cy-888/OpeN64/OpeN64/OpeN64.kicad_sch

## KiCad design OpeN64/OpeN64.kicad_sch (2026-04-06)

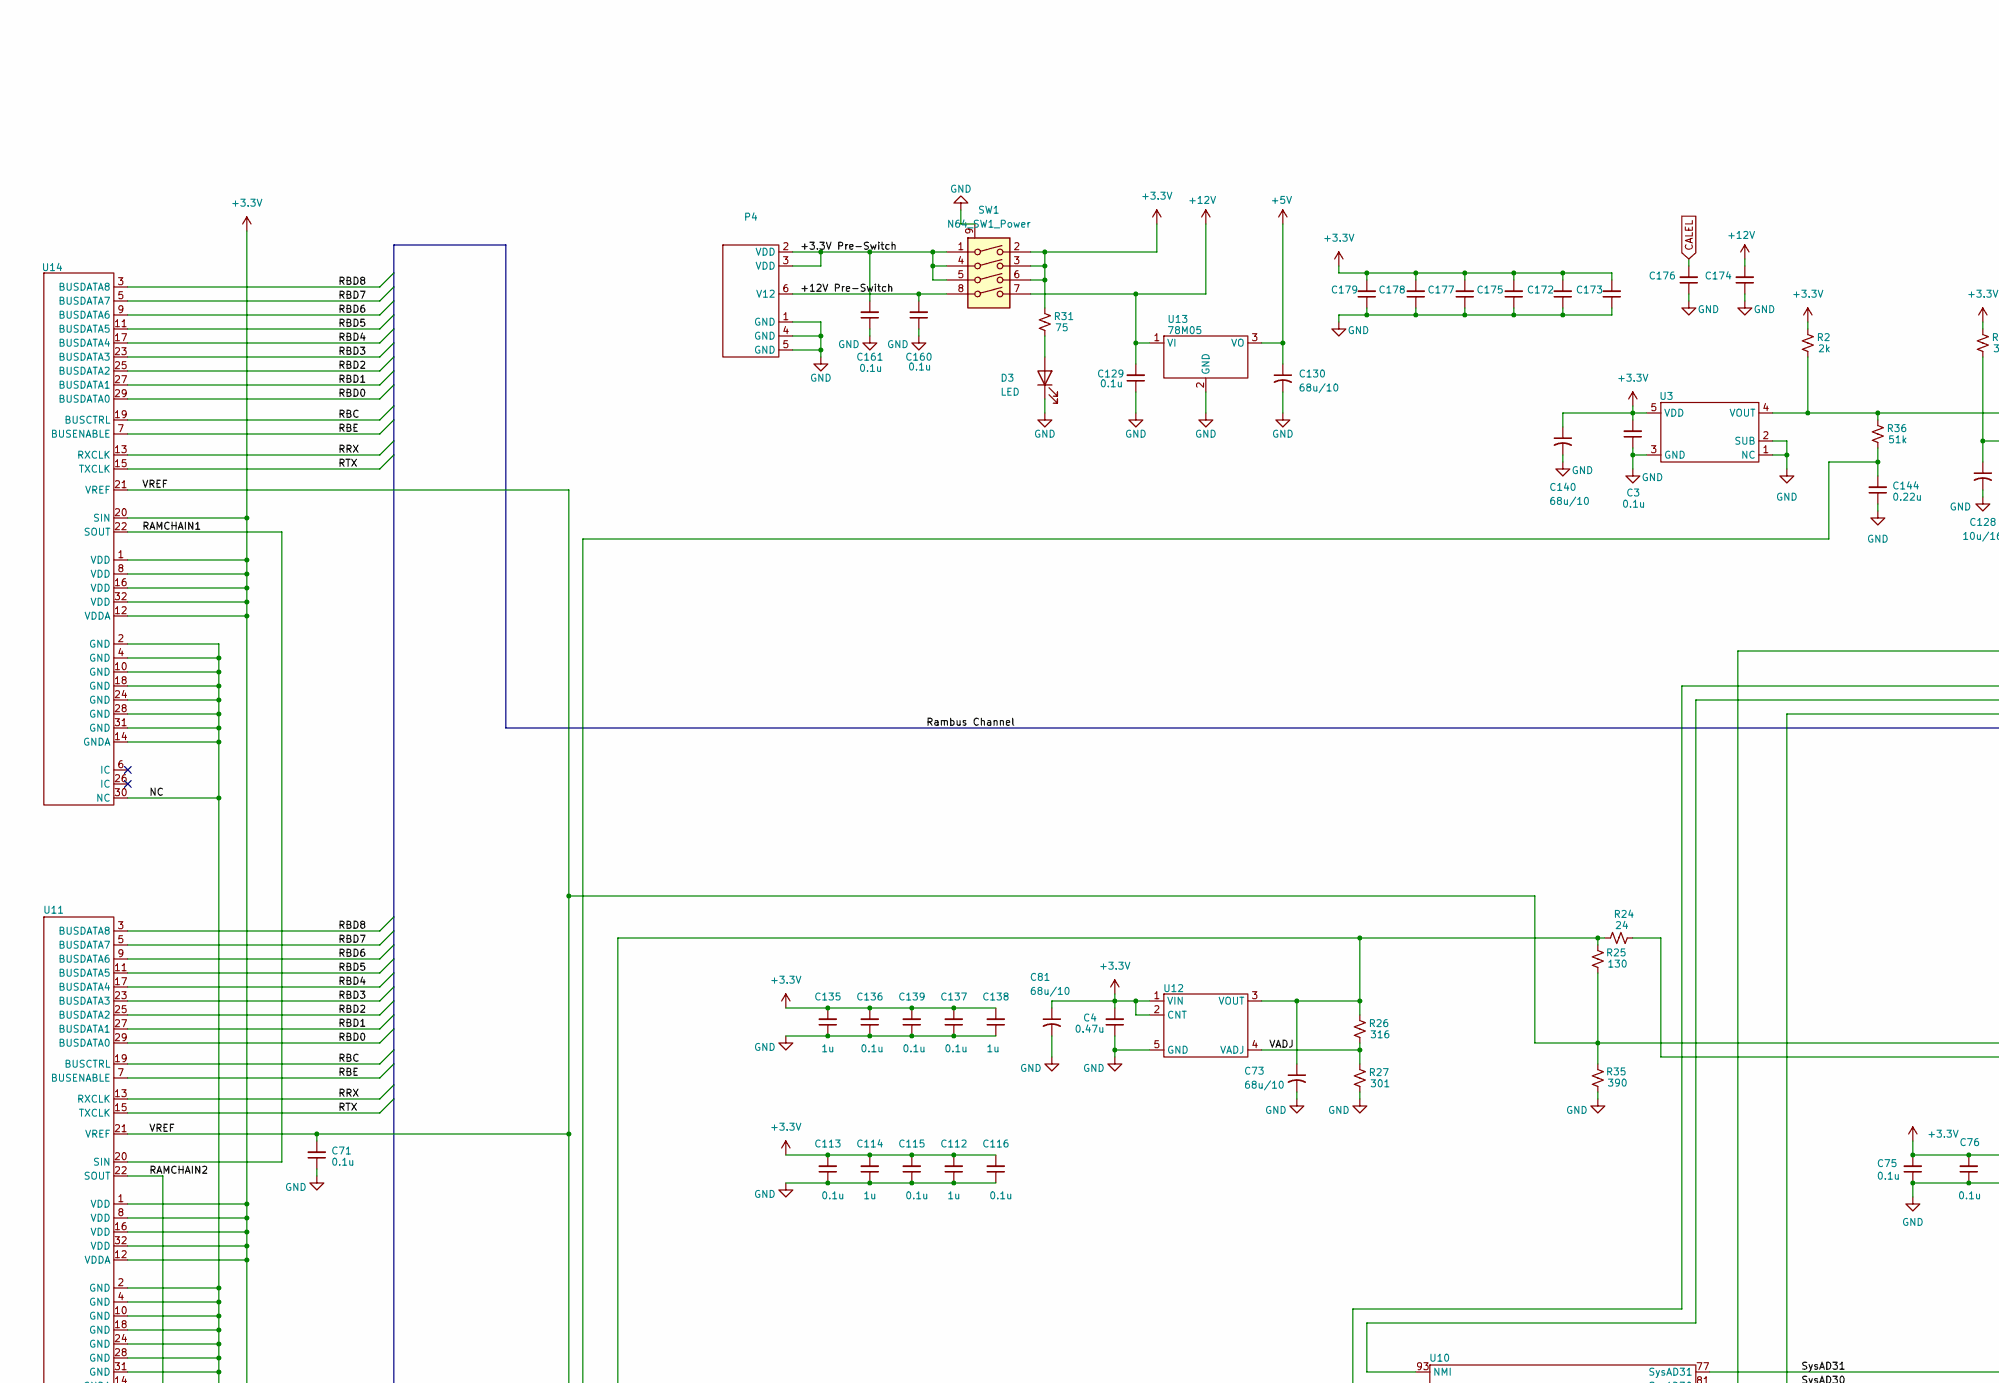
[picture p9: schematic OpeN64.kicad_sch, part in row 1, column 1]

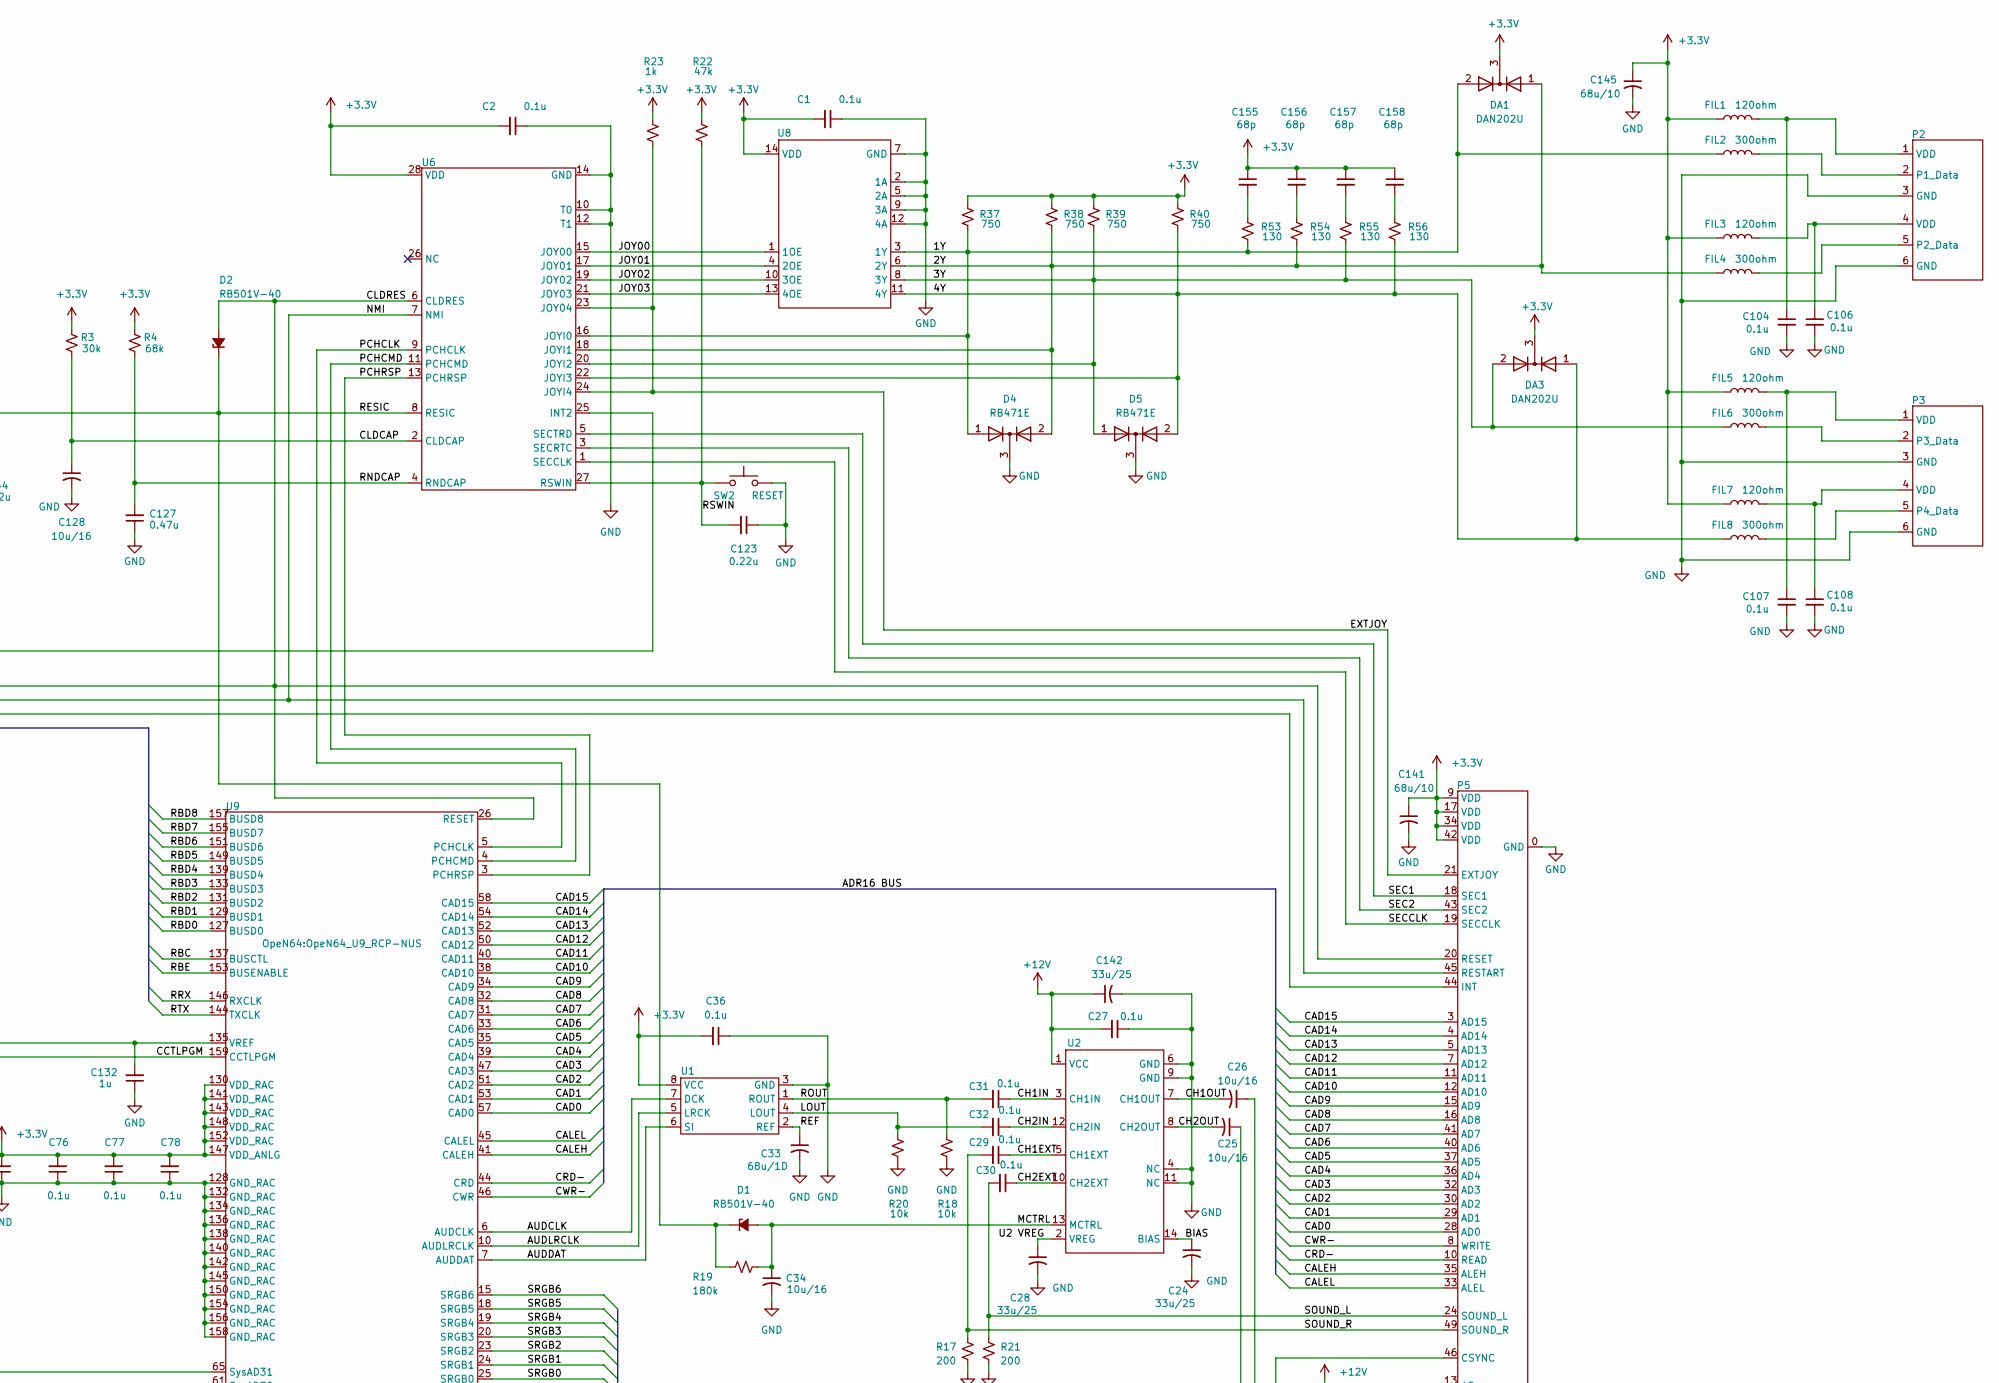
[picture p10: schematic OpeN64.kicad_sch, part in row 1, column 2]

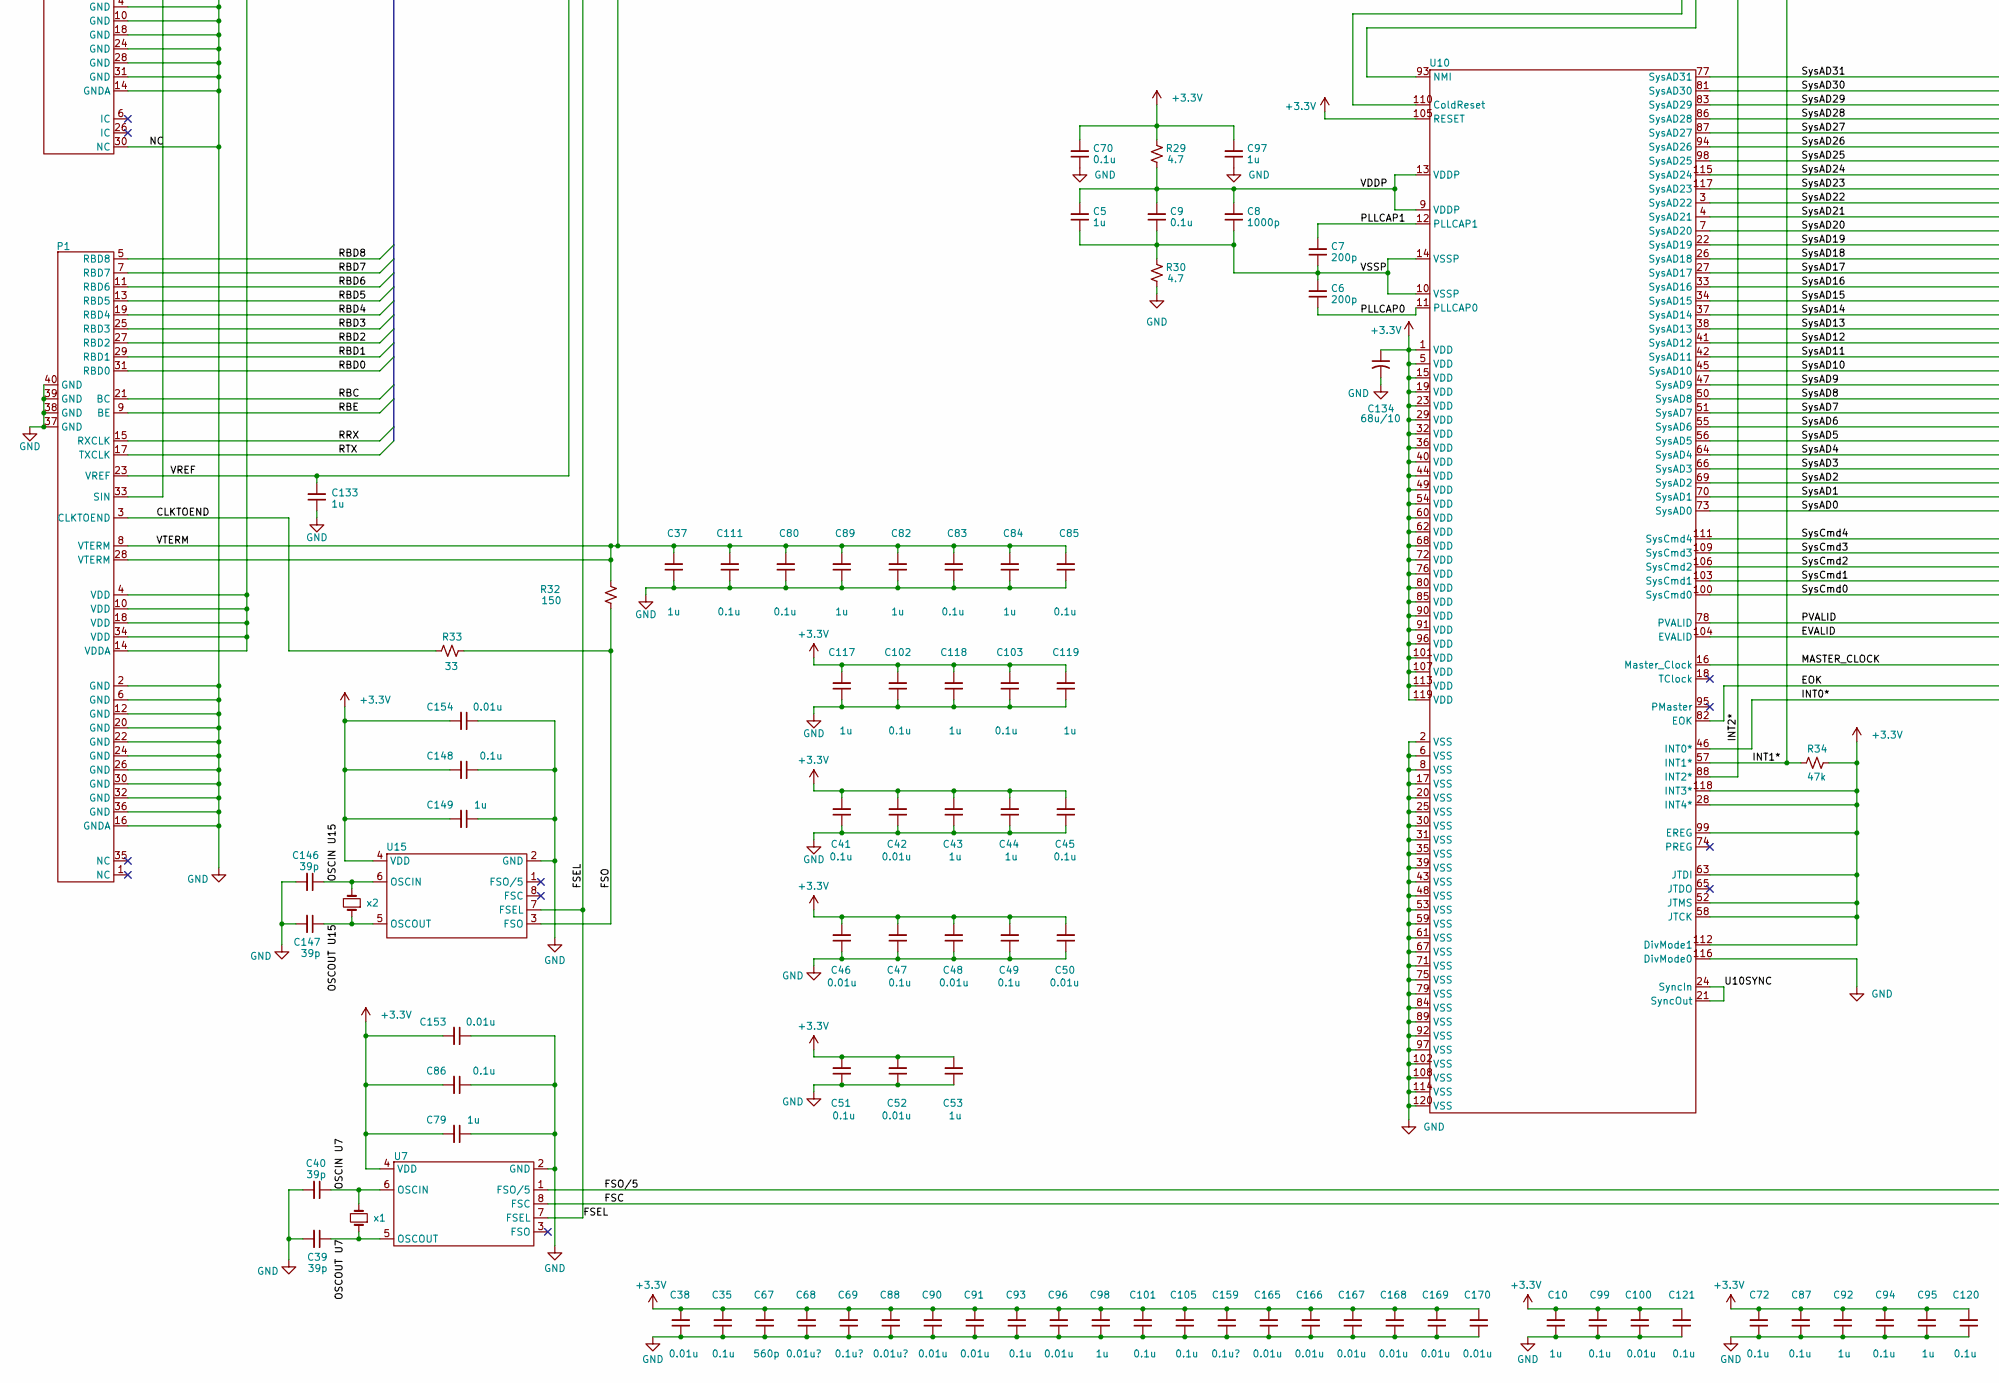
[picture p11: schematic OpeN64.kicad_sch, part in row 2, column 1]

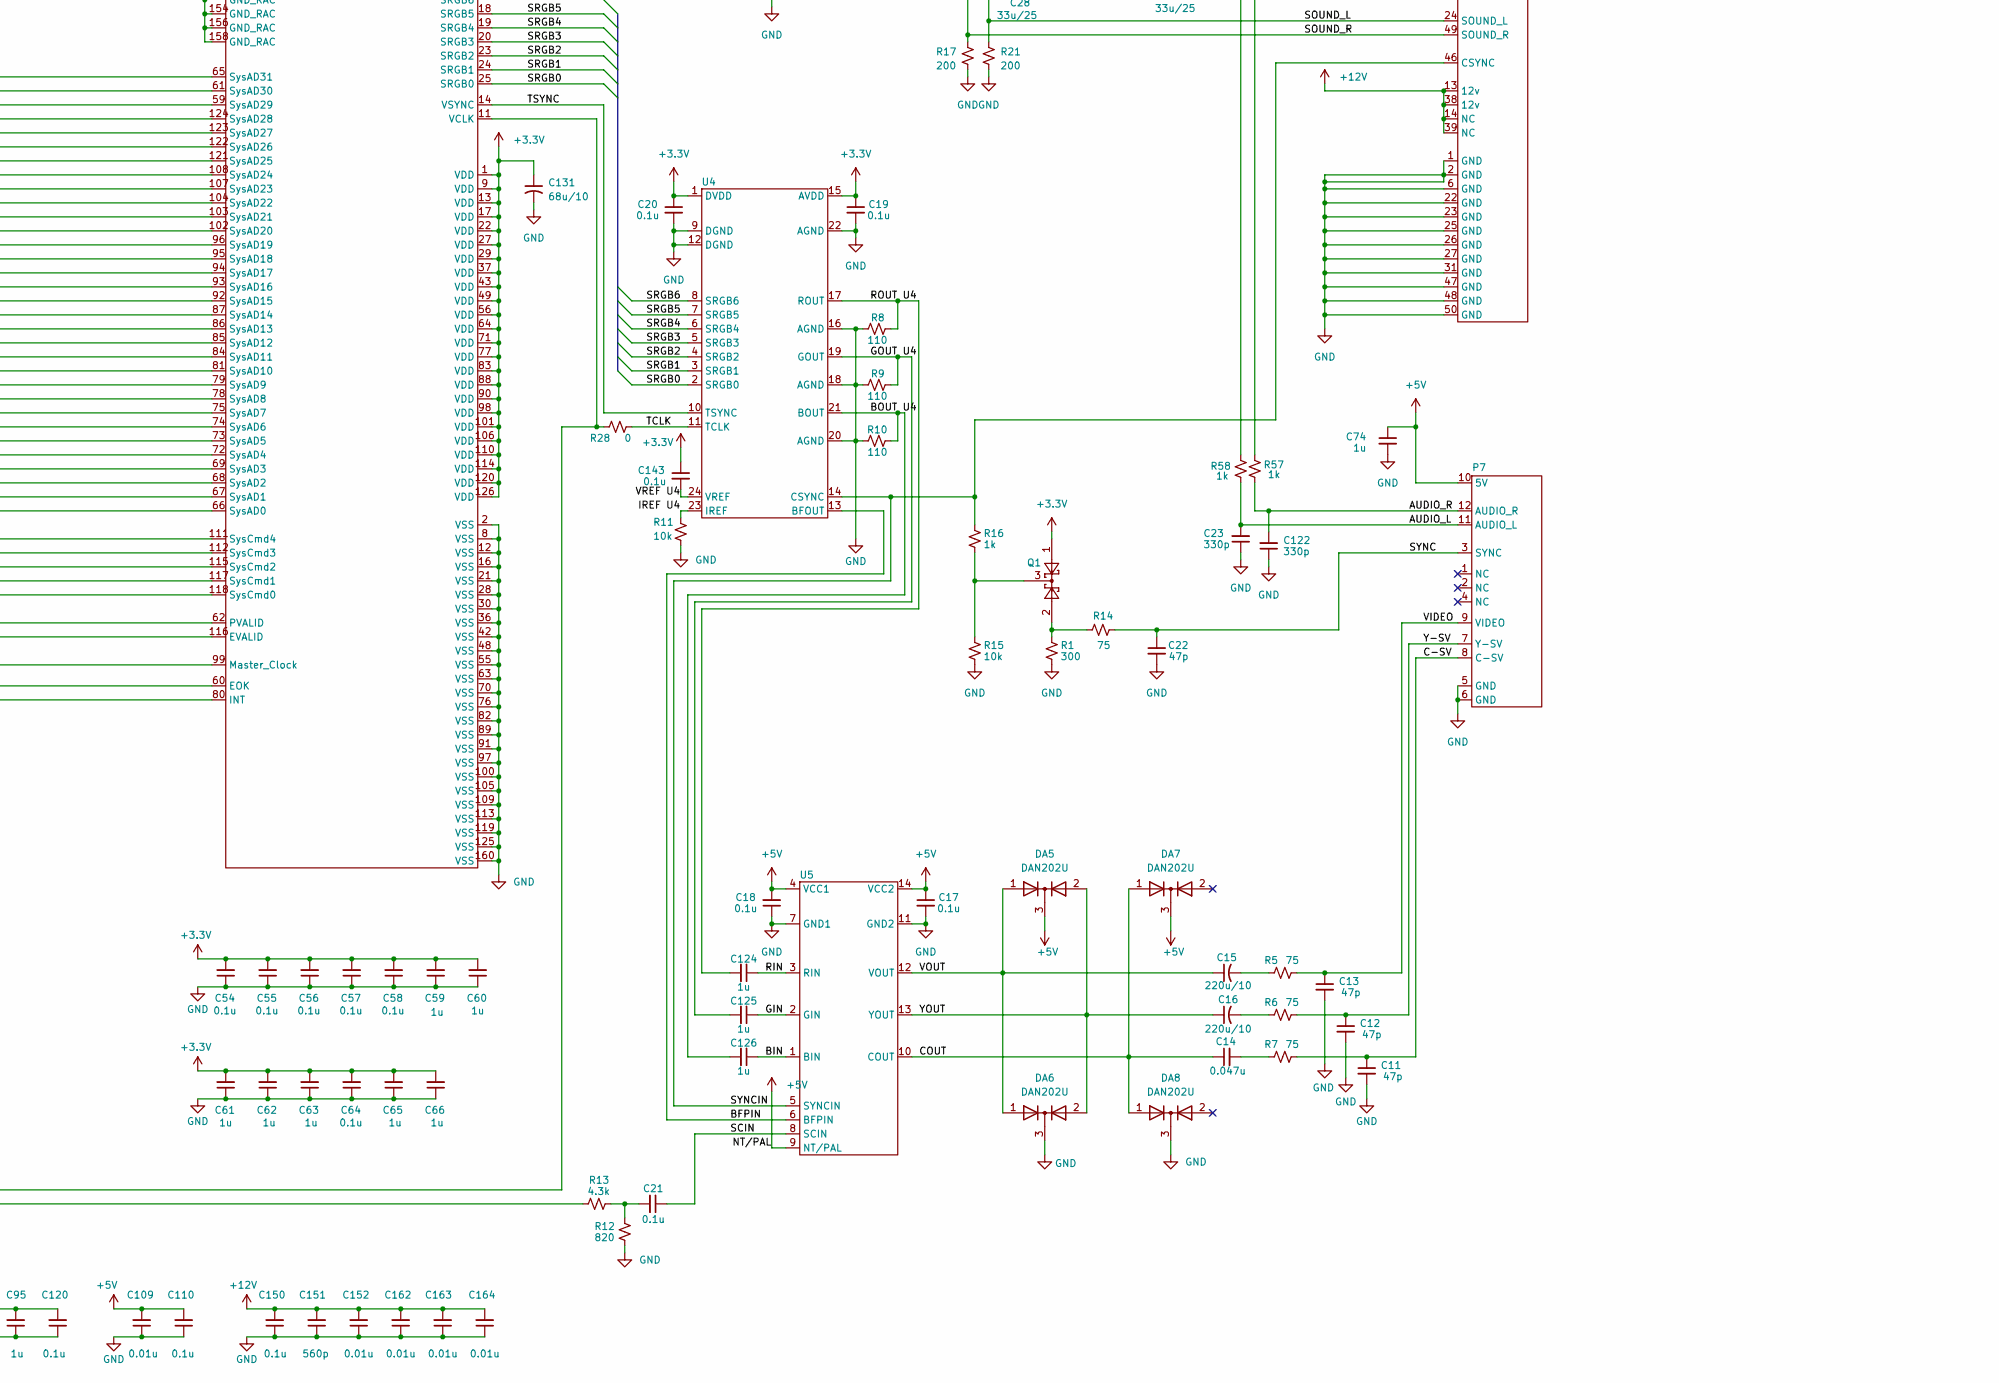
[picture p12: schematic OpeN64.kicad_sch, part in row 2, column 2]

Parts:
C1, C2, C3, C9, C17, C18, C19, C20, C21, C27, C29, C30, C31, C32, C35, C36, C41, C45, C47, C49, C51, C54, C55, C56, C57, C58, C64, C70, C71, C72, C75, C76, C77, C78, C80, C83, C85, C86, C87, C93, C94, C99, C101, C102, C103, C104, C105, C106, C107, C108, C110, C111, C113, C115, C116, C120, C121, C129, C136, C137, C139, C143, C148, C150, C160, C161: 0.1u; OpeN64_SMD_0603
C4, C127: 0.47u; OpeN64_SMD_0603
C5, C10, C37, C43, C44, C53, C59, C60, C61, C62, C63, C65, C66, C74, C79, C82, C84, C89, C92, C95, C97, C98, C112, C114, C117, C118, C119, C124, C125, C126, C132, C133, C135, C138, C149: 1u; OpeN64_SMD_0805
C6, C7: 200p; OpeN64_SMD_0603
C8: 1000p; OpeN64_SMD_0603
C11, C12, C13, C22: 47p; OpeN64_SMD_0603
C14: 0.047u; OpeN64_SMD_0603
C15, C16: 220u/10; OpeN64_CAP_AL_SMD_7.8x4.9
C23, C122: 330p; OpeN64_SMD_0603
C24, C28, C142: 33u/25; OpeN64_CAP_AL_SMD_6.2x4.7
C25, C26: 10u/16; OpeN64_CAP_AL_SMD_3.8x4.5_Flipped
C33: 68u/1D; OpeN64_CAP_AL_SMD_6.2x4.7
C34, C128: 10u/16; OpeN64_CAP_AL_SMD_3.8x4.5
C38, C42, C46, C48, C50, C52, C90, C91, C96, C100, C109, C152, C153, C154, C162, C163, C164, C165, C166, C167, C168, C169, C170: 0.01u; OpeN64_SMD_0603
C39, C40, C146, C147: 39p; OpeN64_SMD_0603
C67, C151: 560p; OpeN64_SMD_0603
C68, C88: 0.01u?; OpeN64_SMD_0603
C69, C159: 0.1u?; OpeN64_SMD_0603
C73, C81, C130, C131, C134, C140, C141, C145: 68u/10; OpeN64_CAP_AL_SMD_6.2x4.7
C123, C144: 0.22u; OpeN64_SMD_0805
C155, C156, C157, C158: 68p; OpeN64_SMD_0603
C172, C176, C177, C178, C179: OpeN64_SMD_0603
C173, C174, C175: OpeN64_SMD_1206
D1, D2: RB501V-40; OpeN64_Diode
D3: LED; OpeN64_D3_Red_LED
D4, D5: RB471E; OpeN64_Diode_Array_5_Pin
DA1, DA3, DA5, DA6, DA7, DA8: DAN202U; OpeN64_Diode_Array
FIL1, FIL3, FIL5, FIL7: 120ohm; OpeN64_Filter
FIL2, FIL4, FIL6, FIL8: 300ohm; OpeN64_Filter
P1: OpeN64_P1_RDRAM_Expansion_Port
P2: OpeN64_P2_Left_Controller_Port
P3: OpeN64_P3_Right_Controller_Port
P4: OpeN64_P4_Power_Port
P6: P5; OpeN64_P5_Cartridge_Slot
P7: OpeN64_P7_Video_Port
Q1: OpeN64_Q_T23
R1: 300; OpeN64_SMD_0603
R2: 2k; OpeN64_SMD_0603
R3: 30k; OpeN64_SMD_0603
R4: 68k; OpeN64_SMD_0603
R5, R6, R7, R14, R31: 75; OpeN64_SMD_0603
R8, R9, R10: 110; OpeN64_SMD_0603
R11, R15, R18, R20: 10k; OpeN64_SMD_0603
R12: 820; OpeN64_SMD_0603
R13: 4.3k; OpeN64_SMD_0603
R16, R23, R57, R58: 1k; OpeN64_SMD_0603
R17, R21: 200; OpeN64_SMD_0603
R19: 180k; OpeN64_SMD_0603
R22, R34: 47k; OpeN64_SMD_0603
R24: 24; OpeN64_SMD_0805
R25: 130; OpeN64_SMD_0805
R26: 316; OpeN64_SMD_0805
R27: 301; OpeN64_SMD_0805
R28: 0; OpeN64_SMD_0603
R29, R30: 4.7; OpeN64_SMD_0805
R32: 150; OpeN64_SMD_0805
R33: 33; OpeN64_SMD_0805
R35: 390; OpeN64_SMD_0805
R36: 51k; OpeN64_SMD_0603
R37, R38, R39, R40: 750; OpeN64_SMD_0603
R53, R54, R55, R56: 130; OpeN64_SMD_0603
SW1: N64_SW1_Power; OpeN64_SW1_Power_Switch
SW2: RESET; OpeN64_SW2_Reset
U1: OpeN64_U1_9480F
U2: OpeN64_U2_AMP_NUS
U3: OpeN64_U3_PST9128
U4: OpeN64_U4_VDC-NUS
U5: OpeN64_U5_ENC-NUS
U6: OpeN64_U6_PIF
U7, U15: OpeN64_U7_15_MX8330
U8: OpeN64_U8_LV125A
U9: OpeN64_U9_RCP-NUS
U10: OpeN64_U10_CPU-NUS
U11, U14: OpeN64_U11_14_RDRAM18-NUS
U12: OpeN64_U12_PQ7VZ5
U13: 78M05; OpeN64_U13_TO-252
x1, x2: Crystal_Small; OpeN64_CRYSTAL_HC49S_TH

Connections:
1Y: D4.1 (A), DA1.2 (A), FIL2.1, R37.2, R53.2, U6.16 (JOYI0), U8.3 (1Y)
2Y: D4.2 (A), DA1.1 (A), FIL4.1, R38.2, R54.2, U6.18 (JOYI1), U8.6 (2Y)
3Y: D5.1 (A), DA3.2 (A), FIL6.1, R39.2, R55.2, U6.20 (JOYI2), U8.8 (3Y)
4Y: D5.2 (A), DA3.1 (A), FIL8.1, R40.2, R56.2, U6.22 (JOYI3), U8.11 (4Y)
+3.3V: C1.2, C2.2, C3.2, C4.2, C10.2, C19.1, C20.1, C35.2, C36.2, C38.2, C41.2, C42.2, C43.2, C44.2, C45.2, C46.2, C47.2, C48.2, C49.2, C50.2, C51.2, C52.2, C53.2, C54.2, C55.2, C56.2, C57.2, C58.2, C59.2, C60.2, C61.2, C62.2, C63.2, C64.2, C65.2, C66.2, C67.2, C68.2, C69.2, C70.2, C72.2, C75.2, C76.2, C77.2, C78.2, C79.2, C81.1, C86.2, C87.2, C88.2, C90.2, C91.2, C92.2, C93.2, C94.2, C95.2, C96.2, C97.2, C98.2, C99.2, C100.2, C101.2, C102.2, C103.2, C105.2, C112.2, C113.2, C114.2, C115.2, C116.2, C117.2, C118.2, C119.2, C120.2, C121.2, C131.1, C134.1, C135.2, C136.2, C137.2, C138.2, C139.2, C140.1, C141.1, C143.1, C145.1, C148.2, C149.2, C153.2, C154.2, C155.1, C156.1, C157.1, C158.1, C159.2, C165.2, C166.2, C167.2, C168.2, C169.2, C170.2, C172.2, C173.2, C175.2, C177.2, C178.2, C179.2, DA1.3 (K), DA3.3 (K), FIL1.1, FIL3.1, FIL5.1, FIL7.1, P1.4 (VDD), P1.10 (VDD), P1.14 (VDDA), P1.18 (VDD), P1.34 (VDD), P6.9 (VDD), P6.17 (VDD), P6.34 (VDD), P6.42 (VDD), Q1.1, R2.1, R3.1, R4.1, R22.1, R23.1, R29.1, R31.1, R34.2, R37.1, R38.1, R39.1, R40.1, SW1.2, SW1.3, SW1.6, U1.8 (VCC), U3.5 (VDD), U4.1 (DVDD), U4.15 (AVDD), U6.28 (VDD), U7.4 (VDD), U8.14 (VDD), U9.1 (VDD), U9.9 (VDD), U9.13 (VDD), U9.17 (VDD), U9.22 (VDD), U9.27 (VDD), U9.29 (VDD), U9.37 (VDD), U9.43 (VDD), U9.49 (VDD), U9.56 (VDD), U9.64 (VDD), U9.71 (VDD), U9.77 (VDD), U9.83 (VDD), U9.88 (VDD), U9.90 (VDD), U9.98 (VDD), U9.101 (VDD), U9.106 (VDD), U9.110 (VDD), U9.114 (VDD), U9.120 (VDD), U9.126 (VDD), U9.130 (VDD_RAC), U9.141 (VDD_RAC), U9.143 (VDD_RAC), U9.147 (VDD_ANLG), U9.148 (VDD_RAC), U9.152 (VDD_RAC), U10.1 (VDD), U10.5 (VDD), U10.15 (VDD), U10.19 (VDD), U10.23 (VDD), U10.28 (INT4*), U10.29 (VDD), U10.32 (VDD), U10.36 (VDD), U10.40 (VDD), U10.44 (VDD), U10.49 (VDD), U10.52 (JTMS), U10.54 (VDD), U10.58 (JTCK), U10.60 (VDD), U10.62 (VDD), U10.63 (JTDI), U10.68 (VDD), U10.72 (VDD), U10.76 (VDD), U10.80 (VDD), U10.85 (VDD), U10.90 (VDD), U10.91 (VDD), U10.96 (VDD), U10.99 (EREG), U10.101 (VDD), U10.105 (RESET), U10.107 (VDD), U10.112 (DivMode1), U10.113 (VDD), U10.118 (INT3*), U10.119 (VDD), U11.1 (VDD), U11.8 (VDD), U11.12 (VDDA), U11.16 (VDD), U11.32 (VDD), U12.1 (VIN), U12.2 (CNT), U14.1 (VDD), U14.8 (VDD), U14.12 (VDDA), U14.16 (VDD), U14.20 (SIN), U14.32 (VDD), U15.4 (VDD)
+3.3V Pre-Switch: C161.2, P4.2 (VDD), P4.3 (VDD), SW1.1, SW1.4, SW1.5
+5V: C17.1, C18.2, C74.1, C109.2, C110.2, C130.1, DA5.3 (K), DA7.3 (K), P7.10 (5V), U5.4 (VCC1), U5.9 (NT/PAL), U5.14 (VCC2), U13.3 (VO)
+12V: C27.2, C129.2, C142.1, C150.2, C151.2, C152.2, C162.2, C163.2, C164.2, C174.2, P6.13 (12v), P6.14 (NC), P6.38 (12v), P6.39 (NC), SW1.7, U2.1 (VCC), U13.1 (VI)
+12V Pre-Switch: C160.2, P4.6 (V12), SW1.8
AUDCLK: U1.7 (DCK), U9.6 (AUDCLK)
AUDDAT: U1.6 (SI), U9.7 (AUDDAT)
AUDIO_L: C23.2, P7.11 (AUDIO_L), R58.2
AUDIO_R: C122.2, P7.12 (AUDIO_R), R57.2
AUDLRCLK: U1.5 (LRCK), U9.10 (AUDLRCLK)
BFPIN: U4.13 (BFOUT), U5.6 (BFPIN)
BIAS: C24.1, U2.14 (BIAS)
BIN: C126.1, U5.1 (BIN)
BOUT U4: C126.2, R10.2, U4.21 (BOUT)
C-SV: C11.1, P7.8 (C-SV), R7.2
CAD0: P6.28 (AD0), U9.57 (CAD0)
CAD1: P6.29 (AD1), U9.53 (CAD1)
CAD2: P6.30 (AD2), U9.51 (CAD2)
CAD3: P6.32 (AD3), U9.47 (CAD3)
CAD4: P6.36 (AD4), U9.39 (CAD4)
CAD5: P6.37 (AD5), U9.35 (CAD5)
CAD6: P6.40 (AD6), U9.33 (CAD6)
CAD7: P6.41 (AD7), U9.31 (CAD7)
CAD8: P6.16 (AD8), U9.32 (CAD8)
CAD9: P6.15 (AD9), U9.34 (CAD9)
CAD10: P6.12 (AD10), U9.38 (CAD10)
CAD11: P6.11 (AD11), U9.40 (CAD11)
CAD12: P6.7 (AD12), U9.50 (CAD12)
CAD13: P6.5 (AD13), U9.52 (CAD13)
CAD14: P6.4 (AD14), U9.54 (CAD14)
CAD15: P6.3 (AD15), U9.58 (CAD15)
CALEH: P6.35 (ALEH), U9.41 (CALEH)
CALEL: C176.2, P6.33 (ALEL), U9.45 (CALEL)
CCTLPGM: R24.2, U9.159 (CCTLPGM)
CH1EXT: C29.1, U2.5 (CH1EXT)
CH1IN: C31.1, U2.3 (CH1IN)
CH1OUT: C26.2, U2.7 (CH1OUT)
CH2EXT: C30.1, U2.10 (CH2EXT)
CH2IN: C32.1, U2.12 (CH2IN)
CH2OUT: C25.2, U2.8 (CH2OUT)
CLDCAP: C128.1, R3.2, U6.2 (CLDCAP)
CLDRES: D2.2 (A), P6.20 (RESET), U6.6 (CLDRES), U9.26 (RESET), U10.110 (ColdReset)
CLKTOEND: P1.3 (CLKTOEND), R33.1
COUT: C14.1, DA7.1 (A), DA8.1 (A), U5.10 (COUT)
CRD-: P6.10 (READ), U9.44 (CRD)
CWR-: P6.8 (WRITE), U9.46 (CWR)
EOK: U9.60 (EOK), U10.82 (EOK)
EVALID: U9.116 (EVALID), U10.104 (EVALID)
EXTJOY: P6.21 (EXTJOY), R23.2, U6.23 (JOY04), U6.24 (JOYI4)
FSC: R13.1, U7.8 (FSC)
FSEL: C144.2, R36.2, U7.7 (FSEL), U15.7 (FSEL)
FSO: R32.2, R33.2, U15.3 (FSO)
FSO/5: R28.1, U7.1 (FSO/5), U9.11 (VCLK)
GIN: C125.1, U5.2 (GIN)
GND: C1.1, C2.1, C3.1, C4.1, C10.1, C11.2, C12.2, C13.2, C17.2, C18.1, C19.2, C20.2, C22.2, C23.1, C24.2, C27.1, C28.2, C33.2, C34.2, C35.1, C36.1, C37.1, C38.1, C39.2, C40.2, C41.1, C42.1, C43.1, C44.1, C45.1, C46.1, C47.1, C48.1, C49.1, C50.1, C51.1, C52.1, C53.1, C54.1, C55.1, C56.1, C57.1, C58.1, C59.1, C60.1, C61.1, C62.1, C63.1, C64.1, C65.1, C66.1, C67.1, C68.1, C69.1, C70.1, C71.1, C72.1, C73.2, C74.2, C75.1, C76.1, C77.1, C78.1, C79.1, C80.1, C81.2, C82.1, C83.1, C84.1, C85.1, C86.1, C87.1, C88.1, C89.1, C90.1, C91.1, C92.1, C93.1, C94.1, C95.1, C96.1, C97.1, C98.1, C99.1, C100.1, C101.1, C102.1, C103.1, C104.2, C105.1, C106.2, C107.2, C108.2, C109.1, C110.1, C111.1, C112.1, C113.1, C114.1, C115.1, C116.1, C117.1, C118.1, C119.1, C120.1, C121.1, C122.1, C123.1, C127.1, C128.2, C129.1, C130.2, C131.2, C132.1, C133.1, C134.2, C135.1, C136.1, C137.1, C138.1, C139.1, C140.2, C141.2, C142.2, C144.1, C145.2, C146.2, C147.2, C148.1, C149.1, C150.1, C151.1, C152.1, C153.1, C154.1, C159.1, C160.1, C161.1, C162.1, C163.1, C164.1, C165.1, C166.1, C167.1, C168.1, C169.1, C170.1, C172.1, C173.1, C174.1, C175.1, C176.1, C177.1, C178.1, C179.1, D3.1 (K), D4.3 (K), D5.3 (K), DA6.3 (K), DA8.3 (K), P1.2 (GND), P1.6 (GND), P1.12 (GND), P1.16 (GNDA), P1.20 (GND), P1.22 (GND), P1.24 (GND), P1.26 (GND), P1.30 (GND), P1.32 (GND), P1.36 (GND), P1.37 (GND), P1.38 (GND), P1.39 (GND), P1.40 (GND), P2.3 (GND), P2.6 (GND), P3.3 (GND), P3.6 (GND), P4.1 (GND), P4.4 (GND), P4.5 (GND), P6.0 (GND), P6.1 (GND), P6.2 (GND), P6.6 (GND), P6.22 (GND), P6.23 (GND), P6.25 (GND), P6.26 (GND), P6.27 (GND), P6.31 (GND), P6.47 (GND), P6.48 (GND), P6.50 (GND), P7.5 (GND), P7.6 (GND), R1.2, R8.1, R9.1, R10.1, R11.2, R12.2, R15.2, R17.2, R18.2, R20.2, R21.2, R27.2, R30.2, R35.2, SW1.9 (GND), SW2.3 (B), SW2.4 (B), U1.3 (GND), U2.4 (NC), U2.6 (GND), U2.9 (GND), U2.11 (NC), U3.1 (NC), U3.2 (SUB), U3.3 (GND), U4.9 (DGND), U4.12 (DGND), U4.16 (AGND), U4.18 (AGND), U4.20 (AGND), U4.22 (AGND), U5.7 (GND1), U5.11 (GND2), U6.10 (T0), U6.12 (T1), U6.14 (GND), U7.2 (GND), U8.2 (1A), U8.5 (2A), U8.7 (GND), U8.9 (3A), U8.12 (4A), U9.2 (VSS), U9.8 (VSS), U9.12 (VSS), U9.16 (VSS), U9.21 (VSS), U9.28 (VSS), U9.30 (VSS), U9.36 (VSS), U9.42 (VSS), U9.48 (VSS), U9.55 (VSS), U9.63 (VSS), U9.70 (VSS), U9.76 (VSS), U9.82 (VSS), U9.89 (VSS), U9.91 (VSS), U9.97 (VSS), U9.100 (VSS), U9.105 (VSS), U9.109 (VSS), U9.113 (VSS), U9.119 (VSS), U9.125 (VSS), U9.128 (GND_RAC), U9.132 (GND_RAC), U9.134 (GND_RAC), U9.136 (GND_RAC), U9.138 (GND_RAC), U9.140 (GND_RAC), U9.142 (GND_RAC), U9.145 (GND_RAC), U9.150 (GND_RAC), U9.154 (GND_RAC), U9.156 (GND_RAC), U9.158 (GND_RAC), U9.160 (VSS), U10.2 (VSS), U10.6 (VSS), U10.8 (VSS), U10.17 (VSS), U10.20 (VSS), U10.25 (VSS), U10.30 (VSS), U10.31 (VSS), U10.35 (VSS), U10.39 (VSS), U10.43 (VSS), U10.48 (VSS), U10.53 (VSS), U10.59 (VSS), U10.61 (VSS), U10.67 (VSS), U10.71 (VSS), U10.75 (VSS), U10.79 (VSS), U10.84 (VSS), U10.89 (VSS), U10.92 (VSS), U10.97 (VSS), U10.102 (VSS), U10.108 (VSS), U10.114 (VSS), U10.116 (DivMode0), U10.120 (VSS), U11.2 (GND), U11.4 (GND), U11.10 (GND), U11.14 (GNDA), U11.18 (GND), U11.24 (GND), U11.28 (GND), U11.30 (NC), U11.31 (GND), U12.5 (GND), U13.2 (GND), U14.2 (GND), U14.4 (GND), U14.10 (GND), U14.14 (GNDA), U14.18 (GND), U14.24 (GND), U14.28 (GND), U14.30 (NC), U14.31 (GND), U15.2 (GND)
GOUT U4: C125.2, R9.2, U4.19 (GOUT)
INT0*: U9.80 (INT), U10.46 (INT0*)
INT1*: P6.44 (INT), R34.1, U10.57 (INT1*)
INT2*: U6.25 (INT2), U10.88 (INT2*)
IREF U4: R11.1, U4.23 (IREF)
JOY00: U6.15 (JOY00), U8.1 (1OE)
JOY01: U6.17 (JOY01), U8.4 (2OE)
JOY02: U6.19 (JOY02), U8.10 (3OE)
JOY03: U6.21 (JOY03), U8.13 (4OE)
LOUT: C32.2, R20.1, U1.4 (LOUT)
MASTER_CLOCK: U9.99 (Master_Clock), U10.16 (Master_Clock)
MCTRL: C34.1, D1.2 (A), R19.2, U2.13 (MCTRL)
NMI: P6.45 (RESTART), U6.7 (NMI), U10.93 (NMI)
unnamed: C14.2, R7.1
unnamed: C15.2, R5.1
unnamed: C16.2, R6.1
unnamed: C21.2, R12.1, R13.2
unnamed: C25.1, R58.1
unnamed: C26.1, R57.1
unnamed: C104.1, FIL1.2, P2.1 (VDD)
unnamed: C106.1, FIL3.2, P2.4 (VDD)
unnamed: C107.1, FIL5.2, P3.1 (VDD)
unnamed: C108.1, FIL7.2, P3.4 (VDD)
unnamed: C155.2, R53.1
unnamed: C156.2, R54.1
unnamed: C157.2, R55.1
unnamed: C158.2, R56.1
unnamed: D3.2 (A), R31.2
unnamed: FIL2.2, P2.2 (P1_Data)
unnamed: FIL4.2, P2.5 (P2_Data)
unnamed: FIL6.2, P3.2 (P3_Data)
unnamed: FIL8.2, P3.5 (P4_Data)
unnamed: Q1.2, R1.1, R14.2
unnamed: Q1.3, R15.1, R16.2
OSCIN U7: C40.1, U7.6 (OSCIN), x1.2
OSCIN U15: C146.1, U15.6 (OSCIN), x2.2
OSCOUT U7: C39.1, U7.5 (OSCOUT), x1.1
OSCOUT U15: C147.1, U15.5 (OSCOUT), x2.1
PCHCLK: U6.9 (PCHCLK), U9.5 (PCHCLK)
PCHCMD: U6.11 (PCHCMD), U9.4 (PCHCMD)
PCHRSP: U6.13 (PCHRSP), U9.3 (PCHRSP)
PLLCAP0: C6.1, U10.11 (PLLCAP0)
PLLCAP1: C7.2, U10.12 (PLLCAP1)
PVALID: U9.62 (PVALID), U10.78 (PVALID)
RAMCHAIN1: U11.20 (SIN), U14.22 (SOUT)
RAMCHAIN2: P1.33 (SIN), U11.22 (SOUT)
RBC: P1.21 (BC), U9.137 (BUSCTL), U11.19 (BUSCTRL), U14.19 (BUSCTRL)
RBD0: P1.31 (RBD0), U9.127 (BUSD0), U11.29 (BUSDATA0), U14.29 (BUSDATA0)
RBD1: P1.29 (RBD1), U9.129 (BUSD1), U11.27 (BUSDATA1), U14.27 (BUSDATA1)
RBD2: P1.27 (RBD2), U9.131 (BUSD2), U11.25 (BUSDATA2), U14.25 (BUSDATA2)
RBD3: P1.25 (RBD3), U9.133 (BUSD3), U11.23 (BUSDATA3), U14.23 (BUSDATA3)
RBD4: P1.19 (RBD4), U9.139 (BUSD4), U11.17 (BUSDATA4), U14.17 (BUSDATA4)
RBD5: P1.13 (RBD5), U9.149 (BUSD5), U11.11 (BUSDATA5), U14.11 (BUSDATA5)
RBD6: P1.11 (RBD6), U9.151 (BUSD6), U11.9 (BUSDATA6), U14.9 (BUSDATA6)
RBD7: P1.7 (RBD7), U9.155 (BUSD7), U11.5 (BUSDATA7), U14.5 (BUSDATA7)
RBD8: P1.5 (RBD8), U9.157 (BUSD8), U11.3 (BUSDATA8), U14.3 (BUSDATA8)
RBE: P1.9 (BE), U9.153 (BUSENABLE), U11.7 (BUSENABLE), U14.7 (BUSENABLE)
REF: C33.1, U1.2 (REF)
RESIC: D1.1 (K), D2.1 (K), R2.2, R19.1, R36.1, U3.4 (VOUT), U6.8 (RESIC)
RIN: C124.1, U5.3 (RIN)
RNDCAP: C127.2, R4.2, U6.4 (RNDCAP)
ROUT: C31.2, R18.1, U1.1 (ROUT)
ROUT U4: C124.2, R8.2, U4.17 (ROUT)
RRX: P1.15 (RXCLK), U9.146 (RXCLK), U11.13 (RXCLK), U14.13 (RXCLK)
RSWIN: C123.2, R22.2, SW2.1 (A), SW2.2 (A), U6.27 (RSWIN)
RTX: P1.17 (TXCLK), U9.144 (TXCLK), U11.15 (TXCLK), U14.15 (TXCLK)
SCIN: C21.1, U5.8 (SCIN)
SEC1: P6.18 (SEC1), U6.5 (SECTRD)
SEC2: P6.43 (SEC2), U6.3 (SECRTC)
SECCLK: P6.19 (SECCLK), U6.1 (SECCLK)
SOUND_L: C30.2, P6.24 (SOUND_L), R21.1
SOUND_R: C29.2, P6.49 (SOUND_R), R17.1
SRGB0: U4.2 (SRGB0), U9.25 (SRGB0)
SRGB1: U4.3 (SRGB1), U9.24 (SRGB1)
SRGB2: U4.4 (SRGB2), U9.23 (SRGB2)
SRGB3: U4.5 (SRGB3), U9.20 (SRGB3)
SRGB4: U4.6 (SRGB4), U9.19 (SRGB4)
SRGB5: U4.7 (SRGB5), U9.18 (SRGB5)
SRGB6: U4.8 (SRGB6), U9.15 (SRGB6)
SYNC: C22.1, P7.3 (SYNC), R14.1
SYNCIN: P6.46 (CSYNC), R16.1, U4.14 (CSYNC), U5.5 (SYNCIN)
SysAD0: U9.66 (SysAD0), U10.73 (SysAD0)
SysAD1: U9.67 (SysAD1), U10.70 (SysAD1)
SysAD2: U9.68 (SysAD2), U10.69 (SysAD2)
SysAD3: U9.69 (SysAD3), U10.66 (SysAD3)
SysAD4: U9.72 (SysAD4), U10.64 (SysAD4)
SysAD5: U9.73 (SysAD5), U10.56 (SysAD5)
SysAD6: U9.74 (SysAD6), U10.55 (SysAD6)
SysAD7: U9.75 (SysAD7), U10.51 (SysAD7)
SysAD8: U9.78 (SysAD8), U10.50 (SysAD8)
SysAD9: U9.79 (SysAD9), U10.47 (SysAD9)
SysAD10: U9.81 (SysAD10), U10.45 (SysAD10)
SysAD11: U9.84 (SysAD11), U10.42 (SysAD11)
SysAD12: U9.85 (SysAD12), U10.41 (SysAD12)
SysAD13: U9.86 (SysAD13), U10.38 (SysAD13)
SysAD14: U9.87 (SysAD14), U10.37 (SysAD14)
SysAD15: U9.92 (SysAD15), U10.34 (SysAD15)
SysAD16: U9.93 (SysAD16), U10.33 (SysAD16)
SysAD17: U9.94 (SysAD17), U10.27 (SysAD17)
SysAD18: U9.95 (SysAD18), U10.26 (SysAD18)
SysAD19: U9.96 (SysAD19), U10.22 (SysAD19)
SysAD20: U9.102 (SysAD20), U10.7 (SysAD20)
SysAD21: U9.103 (SysAD21), U10.4 (SysAD21)
SysAD22: U9.104 (SysAD22), U10.3 (SysAD22)
SysAD23: U9.107 (SysAD23), U10.117 (SysAD23)
SysAD24: U9.108 (SysAD24), U10.115 (SysAD24)
SysAD25: U9.121 (SysAD25), U10.98 (SysAD25)
SysAD26: U9.122 (SysAD26), U10.94 (SysAD26)
SysAD27: U9.123 (SysAD27), U10.87 (SysAD27)
SysAD28: U9.124 (SysAD28), U10.86 (SysAD28)
SysAD29: U9.59 (SysAD29), U10.83 (SysAD29)
SysAD30: U9.61 (SysAD30), U10.81 (SysAD30)
SysAD31: U9.65 (SysAD31), U10.77 (SysAD31)
SysCmd0: U9.118 (SysCmd0), U10.100 (SysCmd0)
SysCmd1: U9.117 (SysCmd1), U10.103 (SysCmd1)
SysCmd2: U9.115 (SysCmd2), U10.106 (SysCmd2)
SysCmd3: U9.112 (SysCmd3), U10.109 (SysCmd3)
SysCmd4: U9.111 (SysCmd4), U10.111 (SysCmd4)
TCLK: R28.2, U4.11 (TCLK)
TSYNC: U4.10 (TSYNC), U9.14 (VSYNC)
U2 VREG: C28.1, U2.2 (VREG)
U10SYNC: U10.21 (SyncOut), U10.24 (SyncIn)
VADJ: R26.2, R27.1, U12.4 (VADJ)
VDDP: C5.2, C8.2, C9.2, R29.2, U10.9 (VDDP), U10.13 (VDDP)
VIDEO: C13.1, P7.9 (VIDEO), R5.2
VOUT: C15.1, DA5.1 (A), DA6.1 (A), U5.12 (VOUT)
VREF: C71.2, C132.2, C133.2, P1.23 (VREF), R25.2, R35.1, U9.135 (VREF), U11.21 (VREF), U14.21 (VREF)
VREF U4: C143.2, U4.24 (VREF)
VSSP: C5.1, C6.2, C7.1, C8.1, C9.1, R30.1, U10.10 (VSSP), U10.14 (VSSP)
VTERM: C37.2, C73.1, C80.2, C82.2, C83.2, C84.2, C85.2, C89.2, C111.2, P1.8 (VTERM), P1.28 (VTERM), R24.1, R25.1, R26.1, R32.1, U12.3 (VOUT)
Y-SV: C12.1, P7.7 (Y-SV), R6.2
YOUT: C16.1, DA5.2 (A), DA6.2 (A), U5.13 (YOUT)
